fablabcb/CitRad-SensorUnit/Software/sensor/noise_floor.cpp

#include "noise_floor.h"

const float global_noiseFloor[1024] = {
    -109.68, -109.47, -109.57, -109.47, -109.76, -109.58, -109.67, -109.6,  -109.75, -109.62, -109.66, -109.49, -109.43,
    -109.29, -109.4,  -109.21, -109.27, -109.07, -109.09, -108.94, -108.99, -108.8,  -108.94, -108.77, -108.9,  -108.66,
    -108.67, -108.48, -108.48, -108.27, -108.48, -108.17, -108.22, -107.9,  -108.11, -107.72, -107.86, -107.54, -107.69,
    -107.47, -107.45, -107.22, -107.37, -106.99, -107.09, -106.98, -106.93, -106.69, -106.64, -106.53, -106.5,  -106.17,
    -106.26, -106.19, -106.25, -106.15, -106.22, -106.1,  -105.97, -105.85, -105.9,  -105.77, -105.63, -105.57, -105.58,
    -105.47, -105.4,  -105.34, -105.38, -105.26, -105.1,  -105.05, -105.17, -104.93, -105.14, -105.19, -105.24, -105.24,
    -105.5,  -105.3,  -105.65, -105.49, -105.81, -105.64, -105.97, -105.62, -106.03, -105.9,  -106.21, -106.1,  -106.31,
    -106.23, -106.42, -106.35, -106.44, -106.36, -106.55, -106.34, -106.52, -106.44, -106.71, -106.36, -106.59, -106.52,
    -106.72, -106.45, -106.77, -106.68, -106.81, -106.61, -106.79, -106.79, -106.86, -106.81, -107.05, -107.03, -107.04,
    -106.97, -106.98, -107.02, -107.03, -106.83, -106.91, -106.85, -106.73, -106.49, -106.65, -106.44, -106.61, -106.32,
    -106.58, -106.49, -106.53, -106.39, -106.5,  -106.42, -106.55, -106.41, -106.54, -106.51, -106.57, -106.5,  -106.64,
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
    -97.81,  -95.3,   -96.68,  -95.89,  -95.14,  -91.85,  -92.09,  -87.24,  -90.53,  -87.9,   -87.25,  -84.42,  -77.73,
    -71.09,  -68.15,  -62.39,  -66.98,  -71.48,  -67.09,  -62.61,  -68.39,  -71.54,  -78.19,  -84.93,  -87.75,  -88.36,
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
